Tamacchi/Tamacchi-Hyperion-Remix/STL Prints/Universal Lid/Single Color Print/7. LE.stl

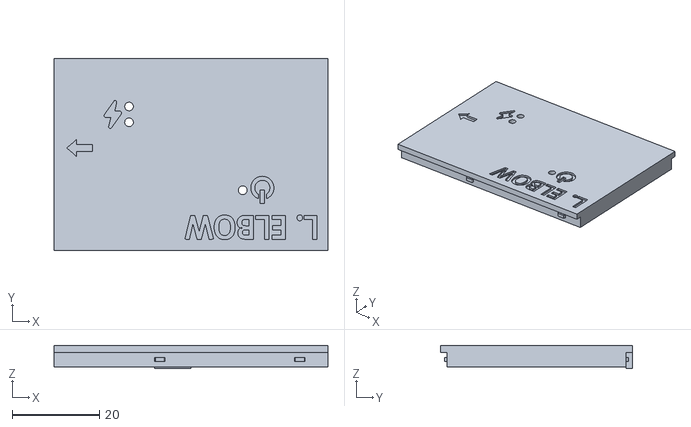
[picture p15: CAD file, 2023-11-28]
STL Prints/Universal Lid/Single Color Print/7. LE.stl
62.8 x 44.0 x 5.37
