Tamacchi/Tamacchi-Hyperion-Remix/STL Prints/Universal Lid/Single Color Print/12. Upper Chest.stl

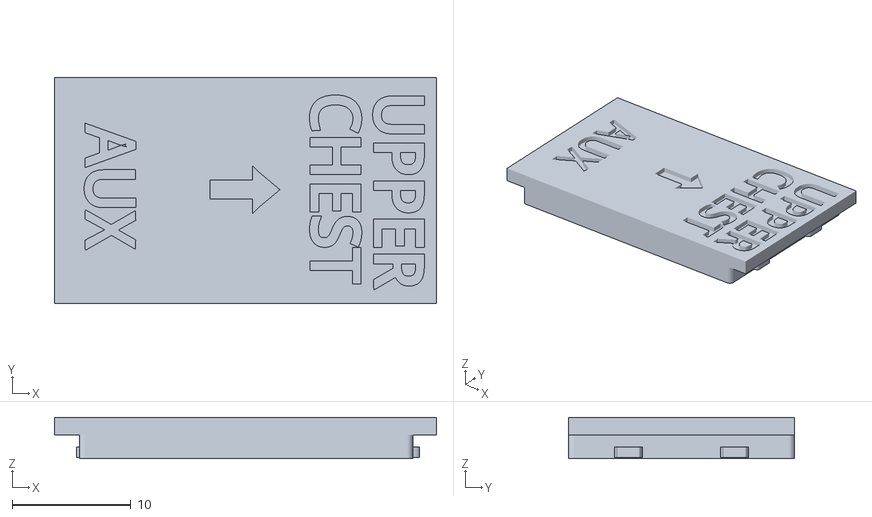
[picture p16: CAD file, 2023-11-28]
STL Prints/Universal Lid/Single Color Print/12. Upper Chest.stl
32.2 x 19.1 x 3.49
